bitfieldlabs/afterglow_pico/pi_pico_code/src/pio.c

/***********************************************************************
 *   ___  ___  ___  ___  ___  ___   _    ___  _ _ _ 
 *  | . || __>|_ _|| __>| . \/  _> | |  | . || | | |
 *  |   || _>  | | | _> |   /| <_/\| |_ | | || | | |
 *  |_|_||_|   |_| |___>|_\_\`____/|___|`___'|__/_/ 
 *                                                  pico
 *      Copyright (c) 2021 bitfield labs
 *
 ***********************************************************************
 *  This file is part of the afterglow pinball LED project:
 *  https://github.com/bitfieldlabs/afterglow_pico
 *
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
 *  You should have received a copy of the GNU Lesser General Public
 *  License along with afterglow.
 *  If not, see <http://www.gnu.org/licenses/>.
 ***********************************************************************/

#include <stdio.h>
#include "pio.h"
#include "hardware/pio.h"
#include "read_col_row.pio.h"
#include "write_col_row.pio.h"
#include "blanking.pio.h"
#include "ws2812.pio.h"
#include "pindef.h"


//------------------------------------------------------------------------------
// Local types

#define ANTI_GHOST_MODE_DETECTION_THRESH 64

typedef enum ANTI_GHOST_MODE_e
{
    ANTI_GHOST_MODE_UNKNOWN = 0,
    ANTI_GHOST_MODE_WPC89_OLD,
    ANTI_GHOST_MODE_WPC95,

    ANTI_GHOST_MODE_LAST
} ANTI_GHOST_MODE_t;


//------------------------------------------------------------------------------
// Local data

// Column/row reading, blanking and WS2812 on PIO 0
static PIO sPioColRow = pio0;
static int sSmCol = -1;
static int sSmRow = -1;
static int sSmBlank = -1;
static int sSmWS2812 = -1;
static int sSmColRowOffset = -1;
static int sSmBlankOffset = -1;
static int sSmWS2812Offset = -1;
static uint8_t sColData = 0;
static uint8_t sRowData = 0;
static uint8_t sColDataPrel = 0; // preliminary column data
static uint8_t sRowDataPrel = 0; // preliminary row data

// Data output on PIO 1
static PIO sPioOutput = pio1;
static int sSmOut = -1;
static int sSmOutOffset = -1;

// Anti-ghosting mode, needs to be identified first
static ANTI_GHOST_MODE_t sAntiGhostMode = ANTI_GHOST_MODE_WPC89_OLD;
static uint8_t sAntiGhostModeId[ANTI_GHOST_MODE_LAST] = {0};


//------------------------------------------------------------------------------
bool pio_init()
{
    // Input/Blanking on PIO 0

    // Find a place for the PIO program in the instruction memory
    sSmColRowOffset = pio_add_program(sPioColRow, &read_col_row_program);
    // Claim an unused state machine for the column reading and run the program
    sSmCol = pio_claim_unused_sm(sPioColRow, true);
    read_col_row_program_init(sPioColRow, sSmCol, sSmColRowOffset, AG_PICO_PIN_LCOL_IN);
    // Claim an unused state machine for the row reading and run the program
    sSmRow = pio_claim_unused_sm(sPioColRow, true);
    read_col_row_program_init(sPioColRow, sSmRow, sSmColRowOffset, AG_PICO_PIN_LROW_IN);
    // Claim an unused state machine for the blanking signal handling program
    sSmBlankOffset = pio_add_program(sPioColRow, &blanking_program);
    sSmBlank = pio_claim_unused_sm(sPioColRow, true);
    blanking_program_init(sPioColRow, sSmBlank, sSmBlankOffset);
    // Claim an unused state machine for the WS2812 control program
    sSmWS2812Offset = pio_add_program(sPioColRow, &ws2812_program);
    sSmWS2812 = pio_claim_unused_sm(sPioColRow, true);
    ws2812_program_init(sPioColRow, sSmWS2812, sSmWS2812Offset, AG_PICO_PIN_WS2812, 800000, true);

    // Lamp matrix output on PIO 1

    // Find a place for the PIO program in the instruction memory
    sSmOutOffset = pio_add_program(sPioOutput, &write_col_row_program);
    // Claim an unused state machine for the column reading and run the program
    sSmOut = pio_claim_unused_sm(sPioOutput, true);
    write_col_row_program_init(sPioOutput, sSmOut, sSmOutOffset);

    return ((sSmCol != -1) && (sSmRow != -1) && (sSmBlank != -1) && (sSmWS2812 != -1) && (sSmOut != -1));
}

//------------------------------------------------------------------------------
uint16_t pio_col_row_data()
{
    // Process all new data
    bool noColData = false;
    bool noRowData = false;
    uint8_t numColData = 0;
    uint8_t numRowData = 0;
    bool waited = false;
    while (!noColData || !noRowData)
    {
        // Check for new row data
        if (sSmRow != -1)
        {
            noRowData = pio_sm_is_rx_fifo_empty(sPioColRow, sSmRow);
            if (!noRowData)
            {
                uint32_t d = pio_sm_get(sPioColRow, sSmRow);
                sRowDataPrel = (uint8_t)((d >> 23) & 0xff);
                numRowData++;
            }
        }

        // Check for new column data
        if (sSmCol != -1)
        {
            noColData = pio_sm_is_rx_fifo_empty(sPioColRow, sSmCol);
            if (!noColData)
            {
                uint32_t d = pio_sm_get(sPioColRow, sSmCol);
                sColDataPrel = (uint8_t)(d >> 24);
                numColData++;
            }
        }

        // wait a bit for new data to arrive - all input should happen
        // within a few microseconds
        if (!waited && noColData && noRowData && ((numColData + numRowData) < 4))
        {
            waited = true;
            noColData = false;
            sleep_us(6);
        }
    }

    // Try to identify the mode
    ANTI_GHOST_MODE_t mode = ANTI_GHOST_MODE_UNKNOWN;
    if ((numColData == 2) && (numRowData == 2))
    {
        mode = ANTI_GHOST_MODE_WPC95;
    }
    else if ((numRowData == 3) && (numColData == 1))
    {
        mode = ANTI_GHOST_MODE_WPC89_OLD;
    }
    
    if ((sAntiGhostMode != ANTI_GHOST_MODE_UNKNOWN) && (mode == sAntiGhostMode) &&
        (sColDataPrel != 0))
    {
        // Adopt the new data
        if ((mode == ANTI_GHOST_MODE_WPC89_OLD) ||
            (mode == ANTI_GHOST_MODE_WPC95))
        {
            sColData = sColDataPrel;
            sRowData = sRowDataPrel;
        }
    }
    // Identify the anti ghosting mode
    else
    {
        // Count successful identifications
        if (mode != ANTI_GHOST_MODE_UNKNOWN)
        {
            for (uint8_t i=0; i<ANTI_GHOST_MODE_LAST; i++)
            {
                if (i==mode)
                {
                    if (sAntiGhostModeId[i]<0xff)
                    {
                        sAntiGhostModeId[i]++;

                        // switch when having enough evidence
                        if (sAntiGhostModeId[i] > ANTI_GHOST_MODE_DETECTION_THRESH)
                        {
                            sAntiGhostMode = mode;
                        }
                    }
                }
                else if (sAntiGhostModeId[i])
                {
                    sAntiGhostModeId[i]--;
                }
            }
        }
    }

    return ((~sColData << 8) | sRowData);
}

//------------------------------------------------------------------------------
void pio_write_col_row_data(uint8_t colData, uint8_t rowData)
{
    if (sSmOut != -1)
    {
        // Anti-ghosting when all data is zero
        if ((colData == 0) && (rowData == 0))
        {
            // The PIO will check for 0xffffffff
            pio_sm_put(sPioOutput, sSmOut, 0xffffffff);
        }
        else
        {
            // The PIO will read the first 8 bits for the row, the next 8 bits for
            // the column. Data output is inverted (HIGH means off).
            // The unused bits must be set to 0xffff as they are used to reset the
            // data lines.
            uint32_t data = 0xffff0000;
            data |= ~((uint32_t)colData << 8) & 0x0000ff00;
            data |= ~((uint32_t)rowData) & 0x000000ff;
            pio_sm_put(sPioOutput, sSmOut, data);
        }
    }
}

//------------------------------------------------------------------------------
void pio_set_ws2812(uint32_t rgb)
{
    pio_sm_put_blocking(sPioColRow, sSmWS2812, rgb << 8u);
}

//------------------------------------------------------------------------------
void pio_debug()
{
    uint8_t pcCol = pio_sm_get_pc(sPioColRow, sSmCol) - sSmColRowOffset;
    uint8_t pcRow = pio_sm_get_pc(sPioColRow, sSmRow) - sSmColRowOffset;
    uint8_t pcWrite = pio_sm_get_pc(sPioOutput, sSmOut) - sSmOutOffset;
    uint8_t pcWS2812 = pio_sm_get_pc(sPioColRow, sSmWS2812) - sSmWS2812Offset;
    printf("PIO pc %d %d %d %d\n", pcCol, pcRow, pcWrite, pcWS2812);
}
